hackerFaruk/thesisApp/control_app/flutter_01.png

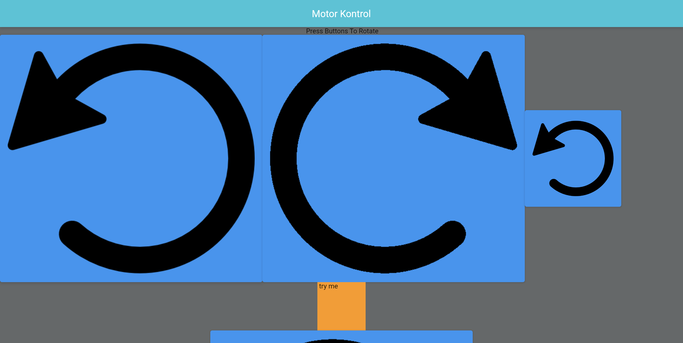
control_app/flutter_01.png
