hackerFaruk/thesisApp/control_app/flutter_02.png

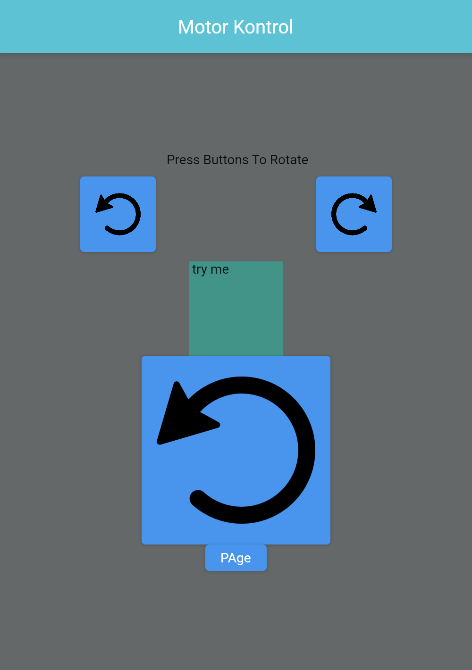
control_app/flutter_02.png
