hackerFaruk/thesisApp/control_app/flutter_03.png

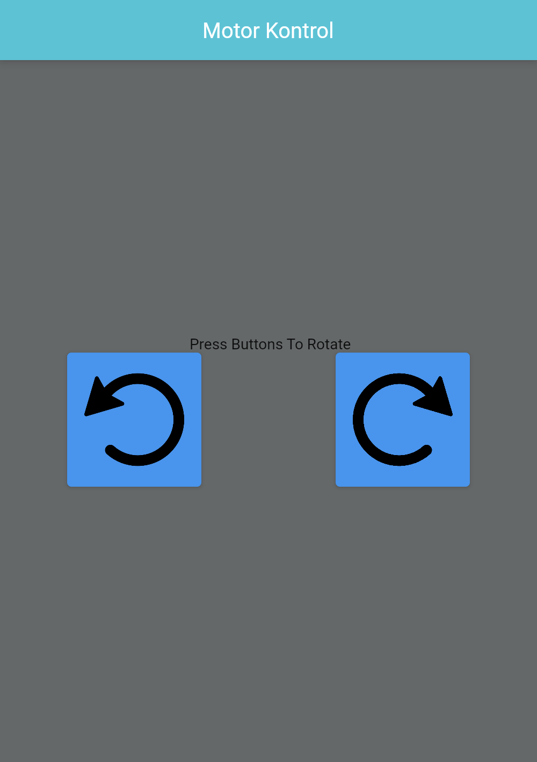
control_app/flutter_03.png
