hackerFaruk/thesisApp/Visuals/deviceModel.png

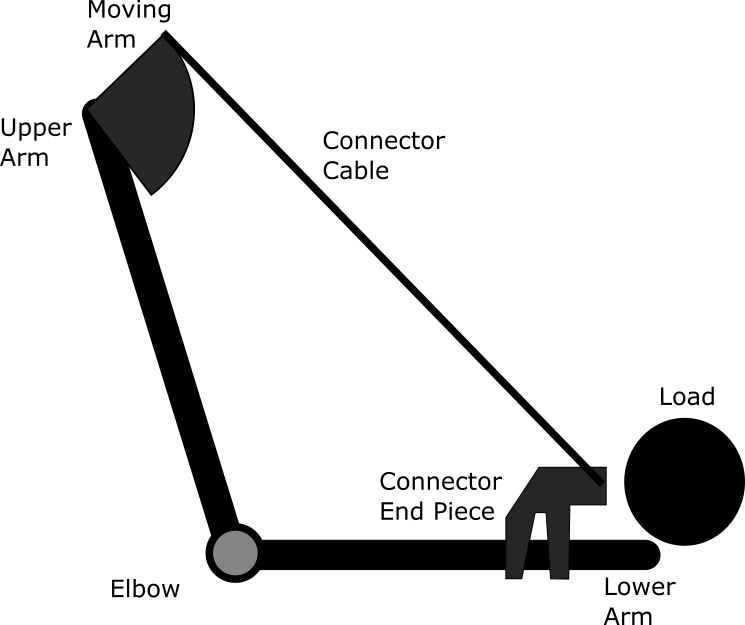
Visuals/deviceModel.png
