hackerFaruk/thesisApp/Visuals/EndPiece.png

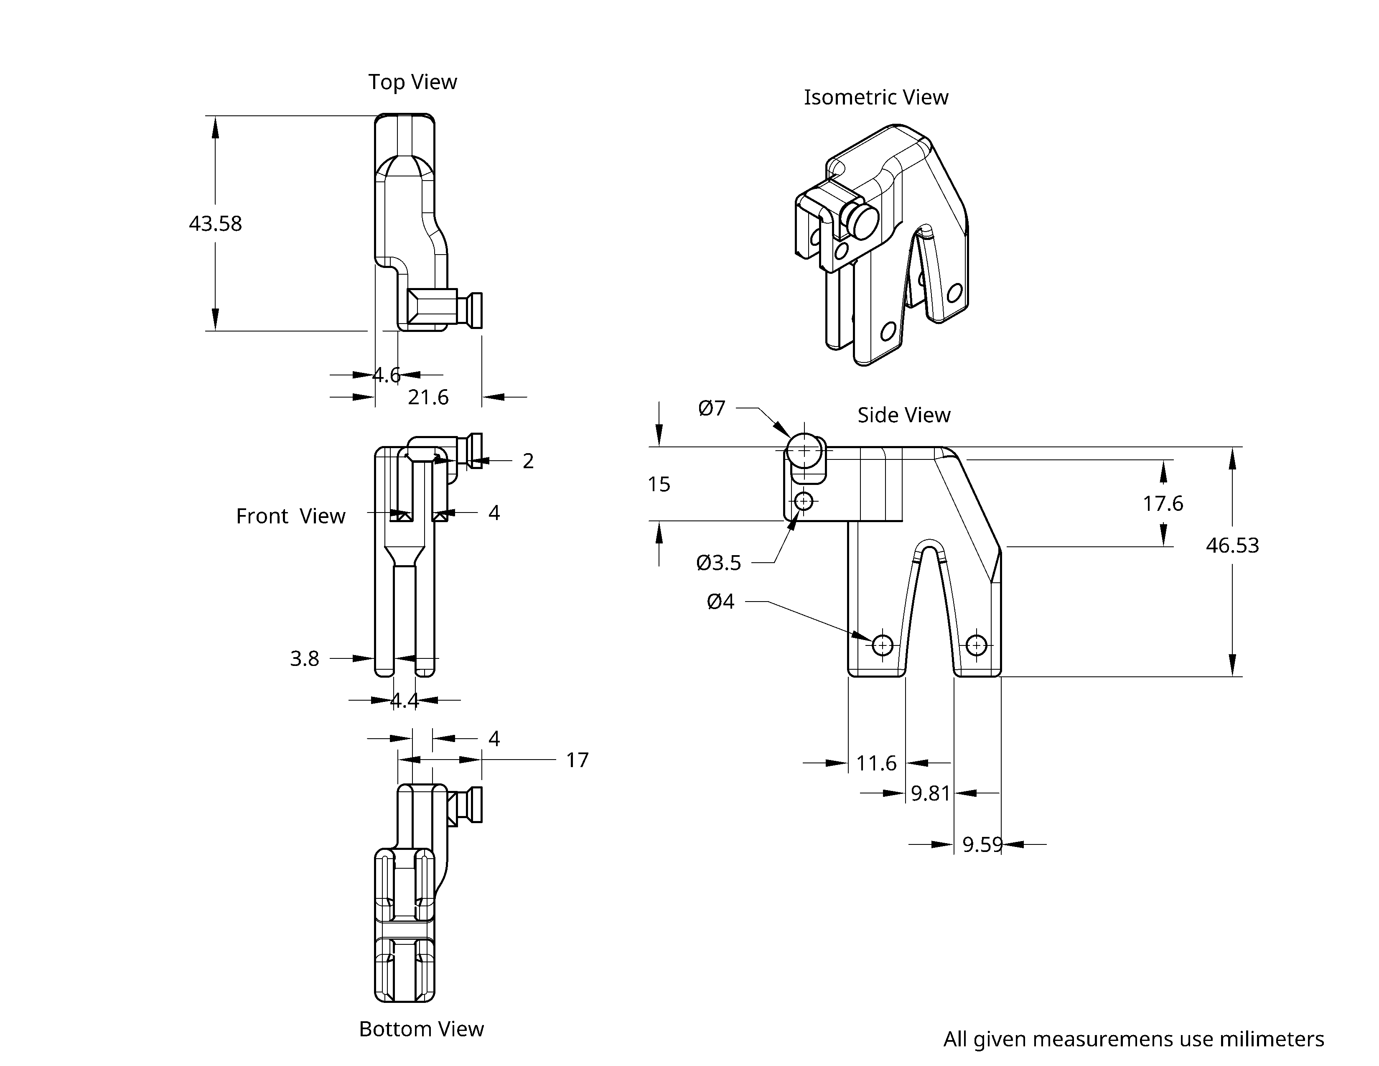
Visuals/EndPiece.png
