hackerFaruk/thesisApp/Visuals/holder.png

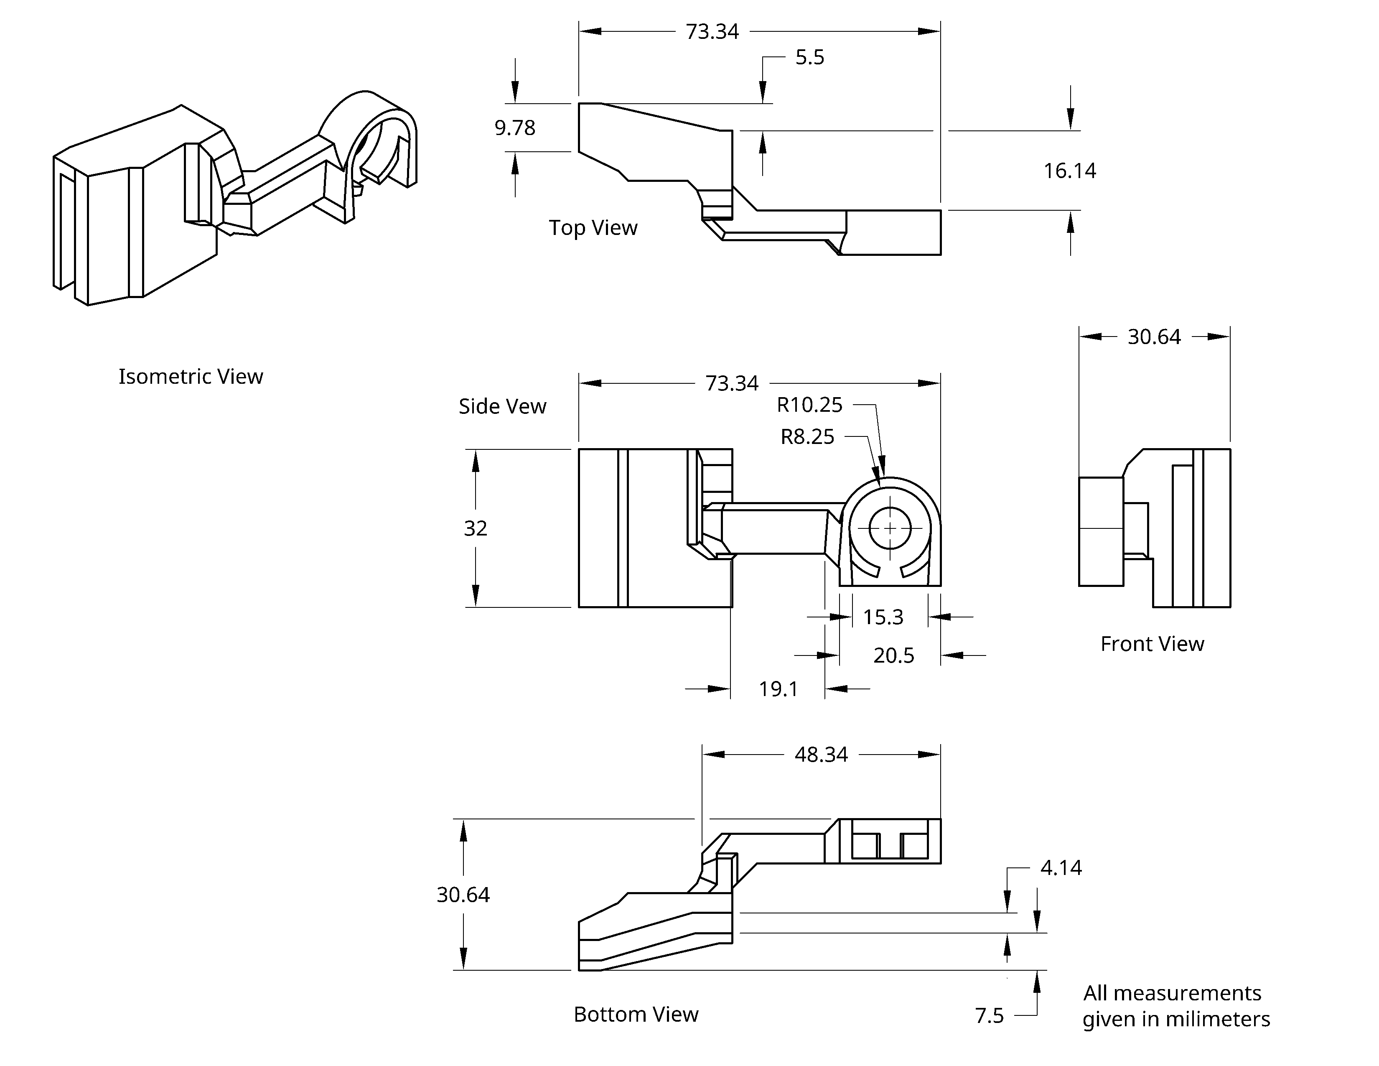
Visuals/holder.png
