hackerFaruk/thesisApp/Visuals/MotorHolder.png

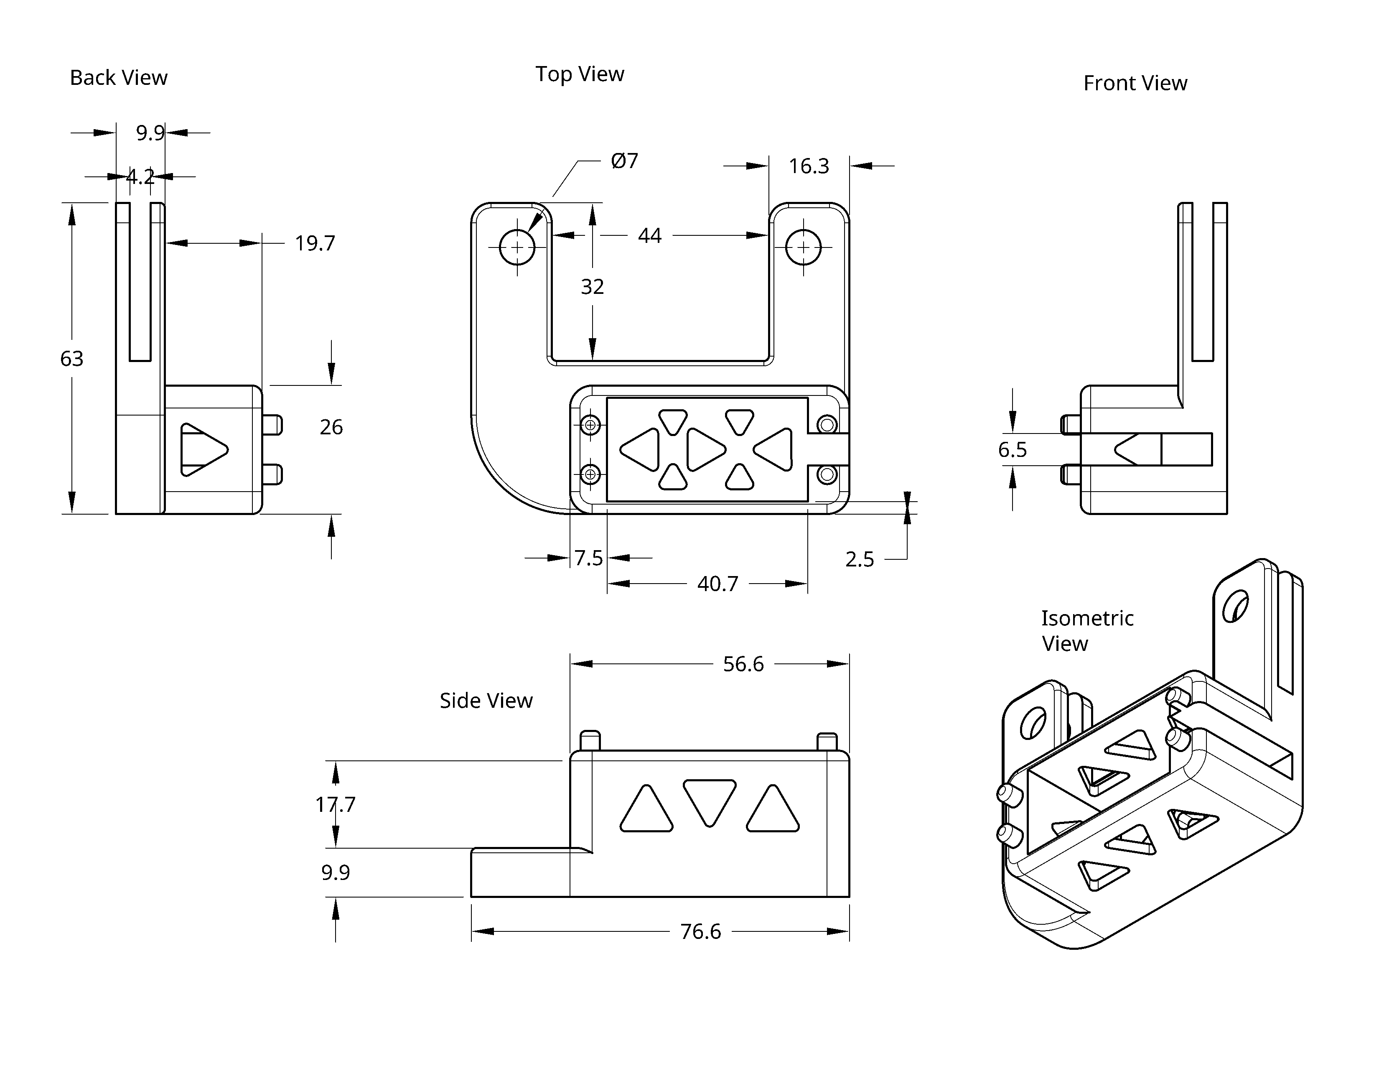
Visuals/MotorHolder.png
