hackerFaruk/thesisApp/Visuals/movingArmdraw.png

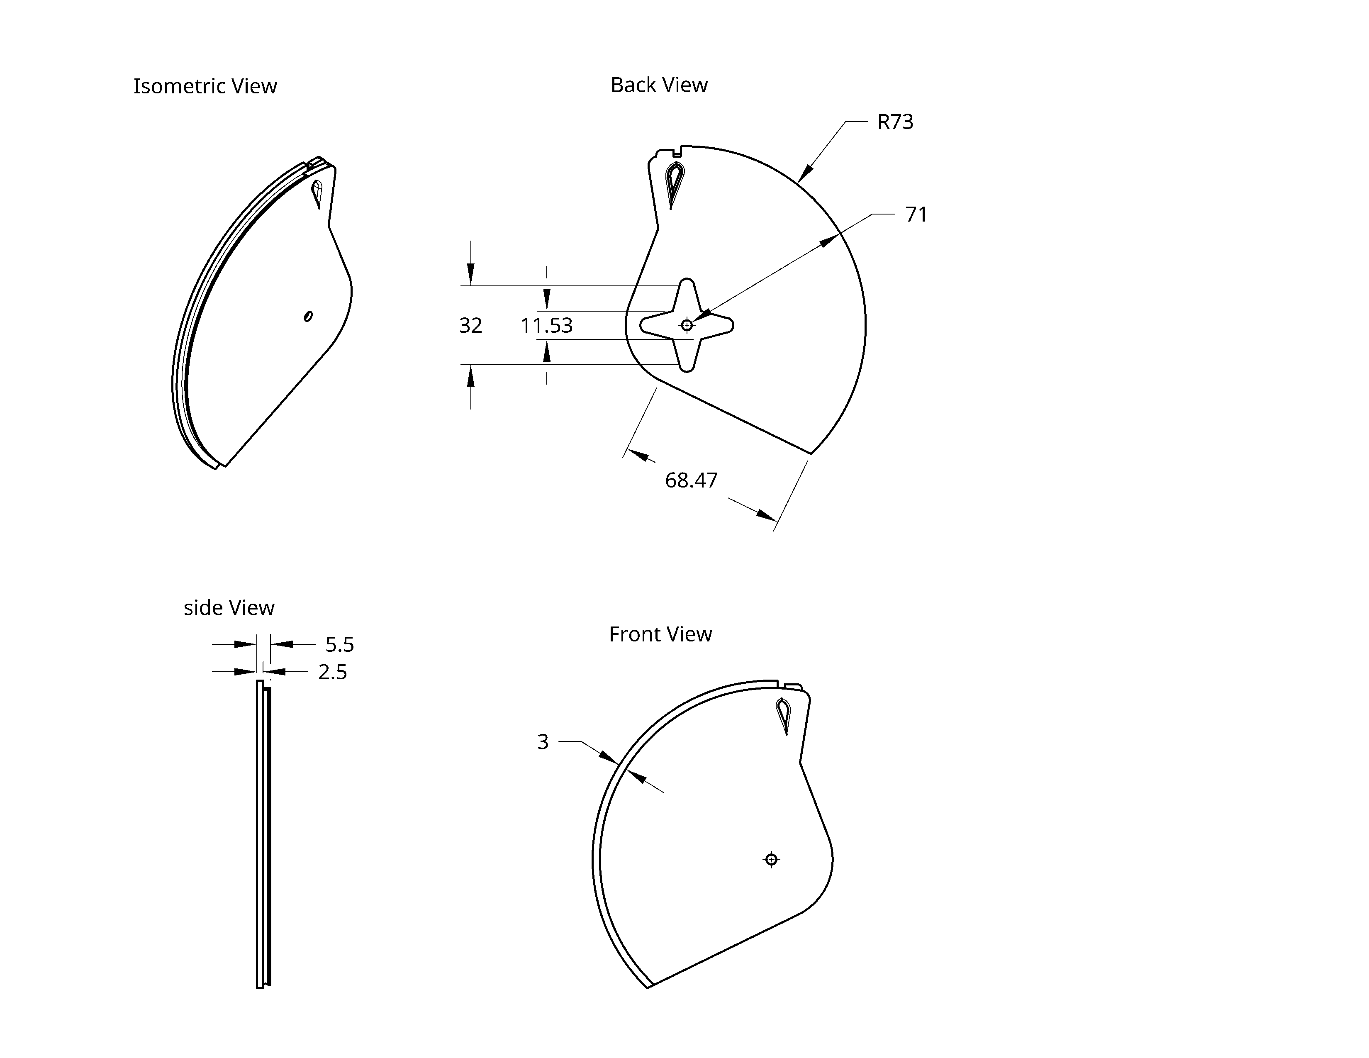
Visuals/movingArmdraw.png
