hackerFaruk/thesisApp/Visuals/pothand.png

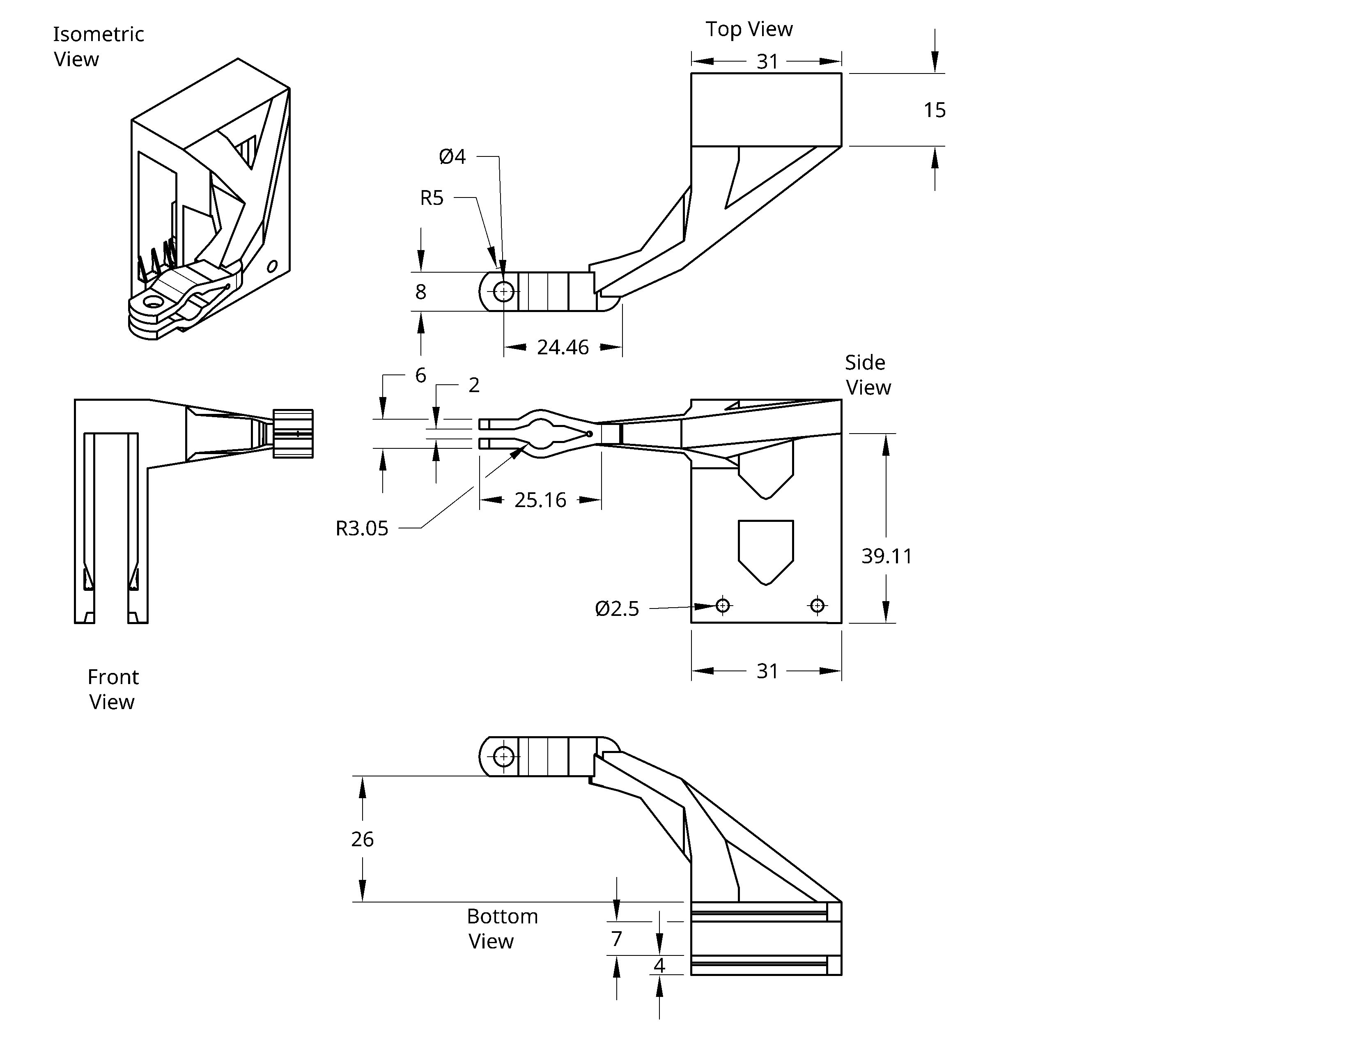
Visuals/pothand.png
